marwantm/esp32-sensor-board/Source Files/Additional Components/3D models/SS-52400-002.step

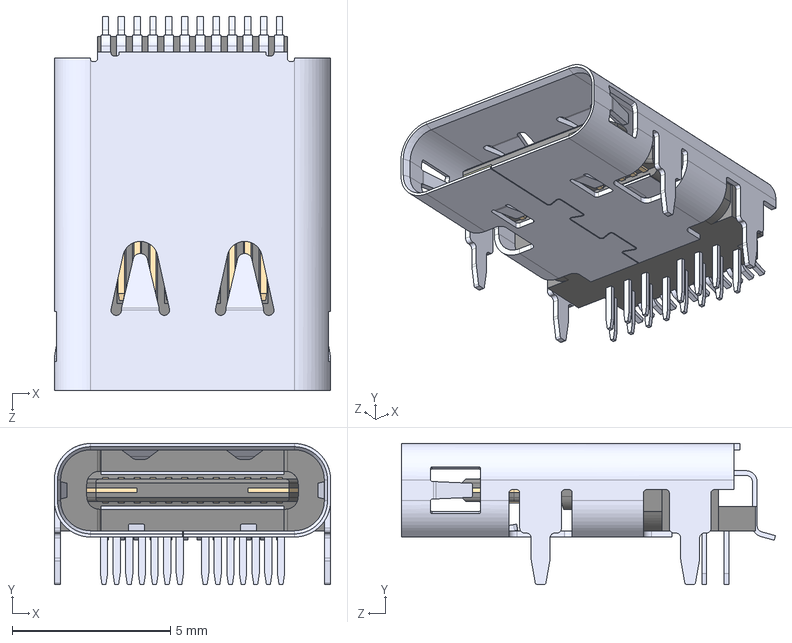
[picture p23: CAD file, 2026-08-19]
Source Files/Additional Components/3D models/SS-52400-002.step
8.74 x 4.46 x 11.8 mm
