marwantm/esp32-sensor-board/Source Files/Additional Components/3D models/ESP32-C3-WROOM-02-H4.step

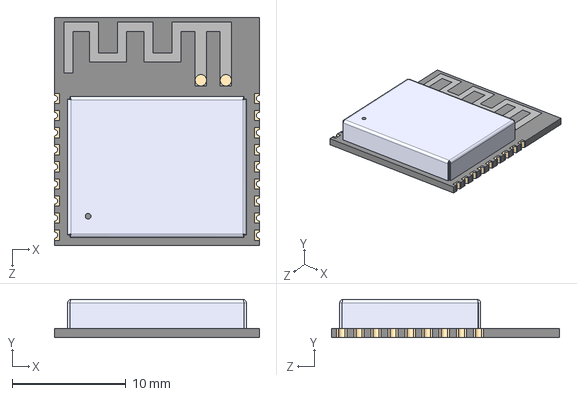
[picture p24: CAD file, 2026-08-19]
Source Files/Additional Components/3D models/ESP32-C3-WROOM-02-H4.step
18.0 x 3.35 x 20.0 mm
