marwantm/esp32-sensor-board/Source Files/Additional Components/3D models/B4B-XH-AM__LF__SN_.step

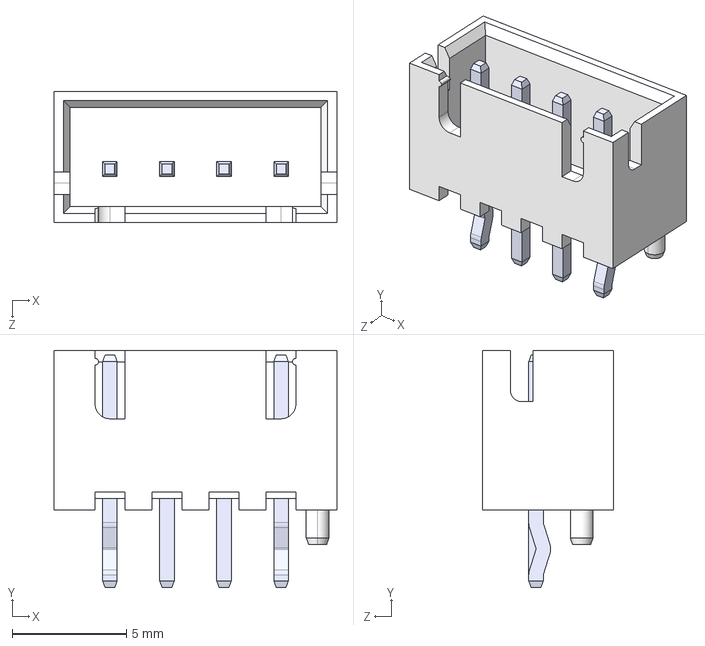
[picture p25: CAD file, 2026-08-19]
Source Files/Additional Components/3D models/B4B-XH-AM__LF__SN_.step
12.4 x 10.4 x 5.75 mm
