marwantm/esp32-sensor-board/Source Files/Additional Components/3D models/SMD-BUTTON_4P-5.2X5.2X1.5MM-SKQGADE010_.step

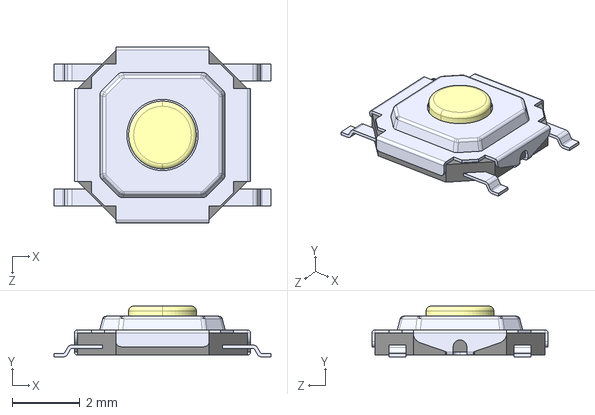
[picture p26: CAD file, 2026-08-19]
Source Files/Additional Components/3D models/SMD-BUTTON_4P-5.2X5.2X1.5MM-SKQGADE010_.step
6.40 x 1.50 x 5.20 mm
